afishyke/DACS/delay_justification/eda_outputs/plots/metric_derivative_energy_by_class.png

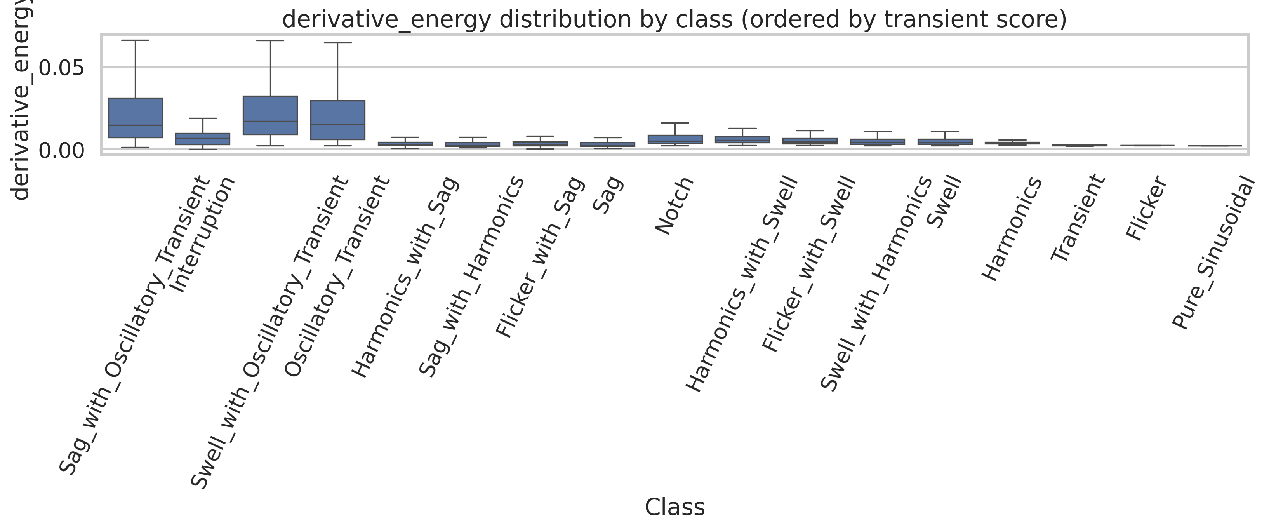
delay_justification/eda_outputs/plots/metric_derivative_energy_by_class.png
