afishyke/DACS/delay_justification/eda_outputs/plots/metric_high_freq_energy_ratio_by_class.png

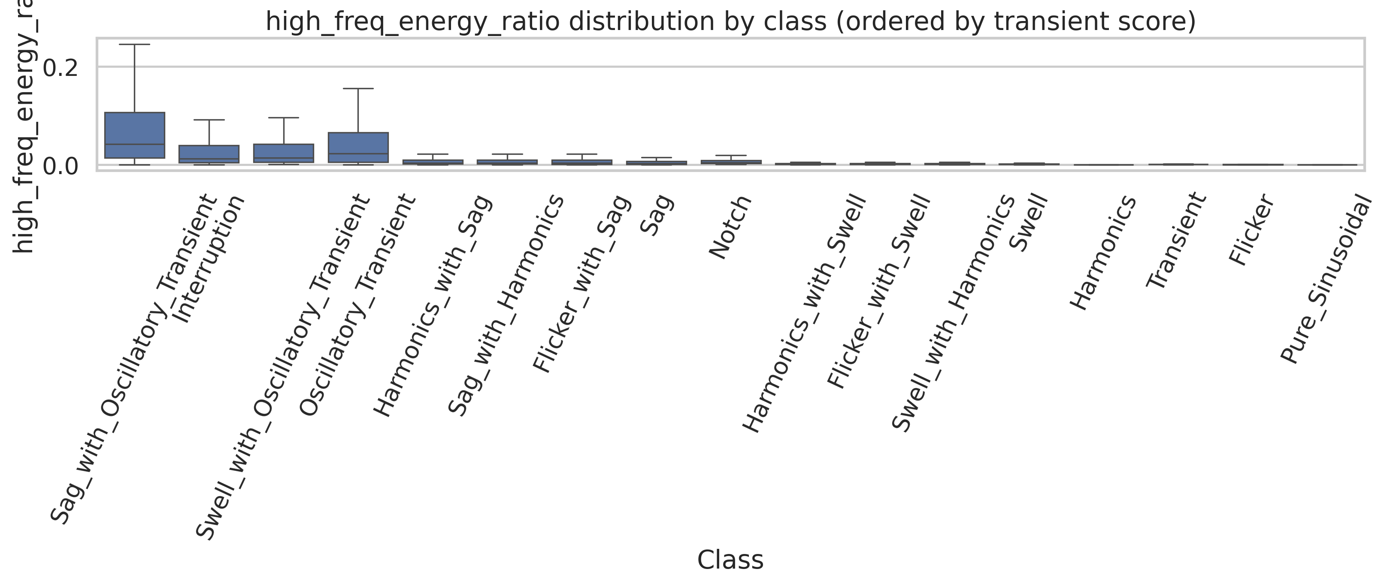
delay_justification/eda_outputs/plots/metric_high_freq_energy_ratio_by_class.png
