afishyke/DACS/delay_justification/eda_outputs/plots/metric_local_peak_change_by_class.png

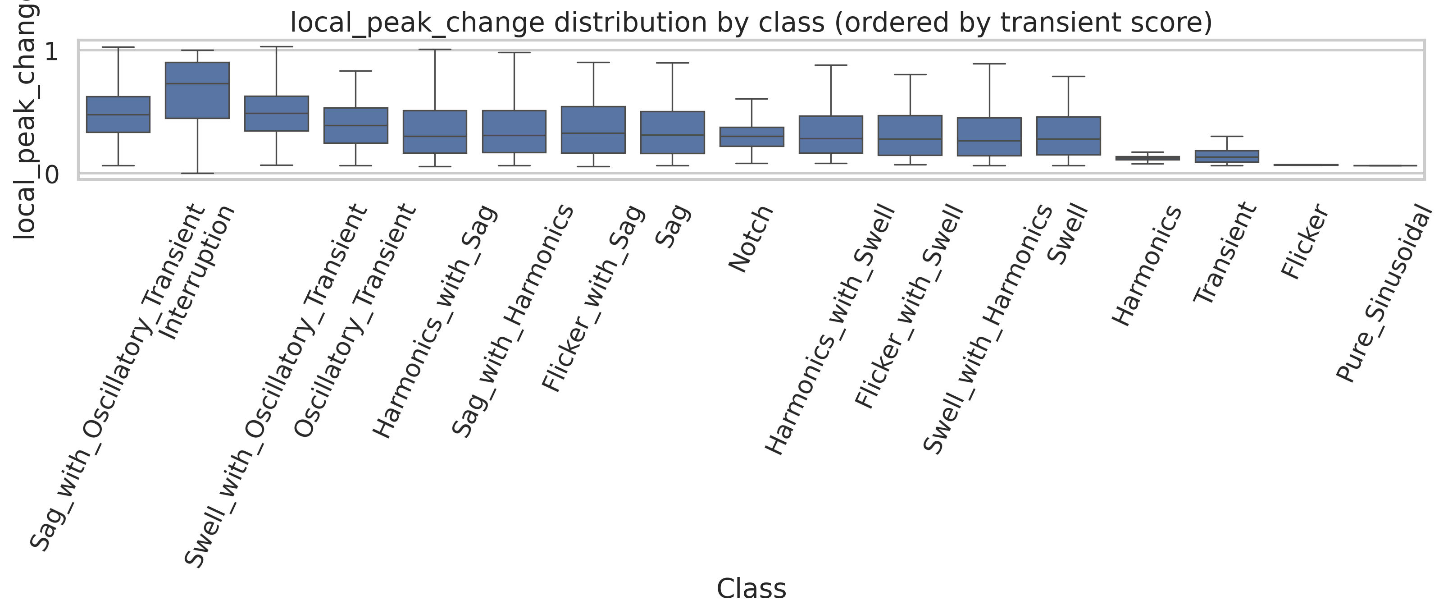
delay_justification/eda_outputs/plots/metric_local_peak_change_by_class.png
