afishyke/DACS/delay_justification/eda_outputs/plots/metric_transient_energy_proxy_by_class.png

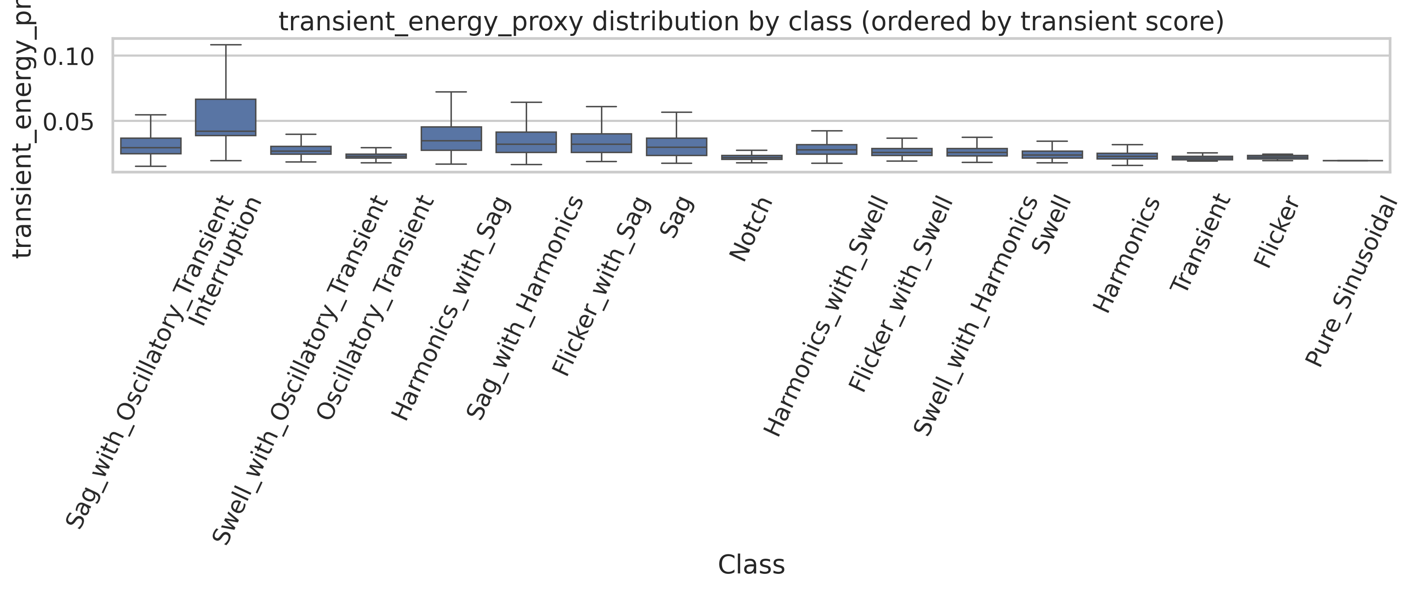
delay_justification/eda_outputs/plots/metric_transient_energy_proxy_by_class.png
