afishyke/DACS/delay_justification/eda_outputs/plots/overlay_harmonics_flicker_related_classes.png

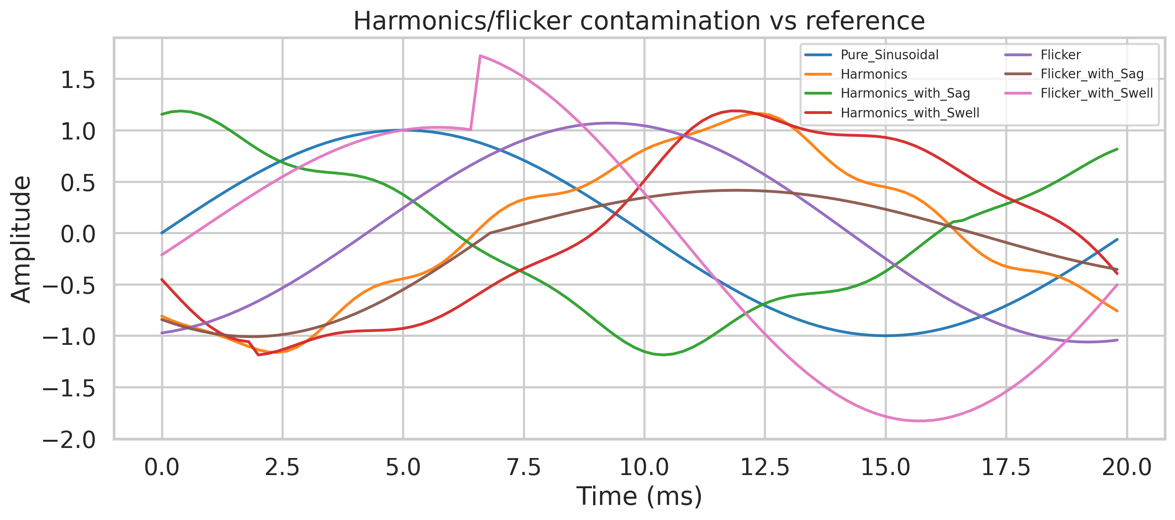
delay_justification/eda_outputs/plots/overlay_harmonics_flicker_related_classes.png
