afishyke/DACS/delay_justification/eda_outputs/plots/overlay_sag_swell_related_classes.png

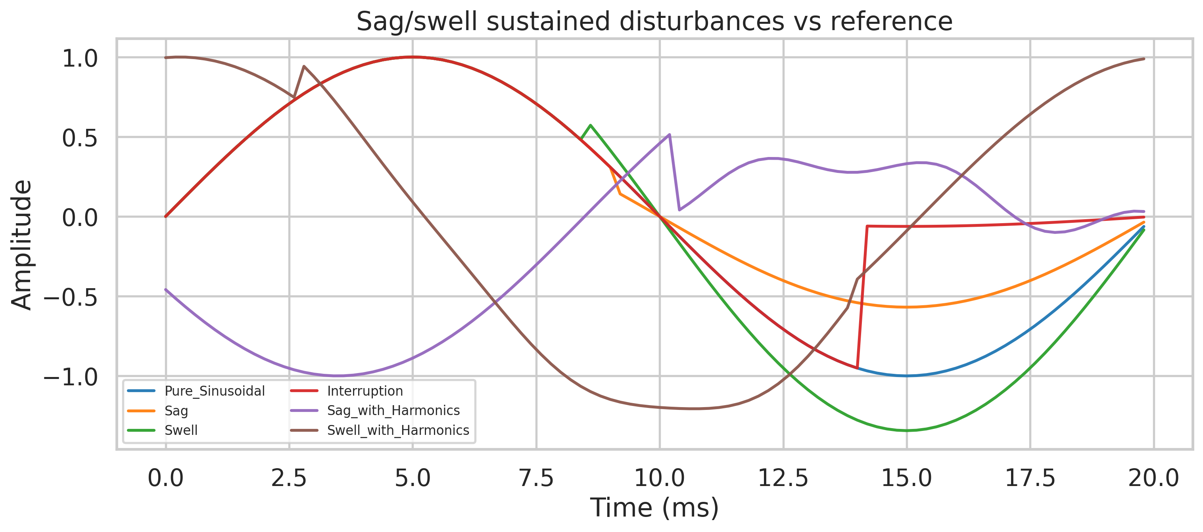
delay_justification/eda_outputs/plots/overlay_sag_swell_related_classes.png
