afishyke/DACS/delay_justification/eda_outputs/plots/per_class_3_representatives/Harmonics_with_Sag_three_representatives.png

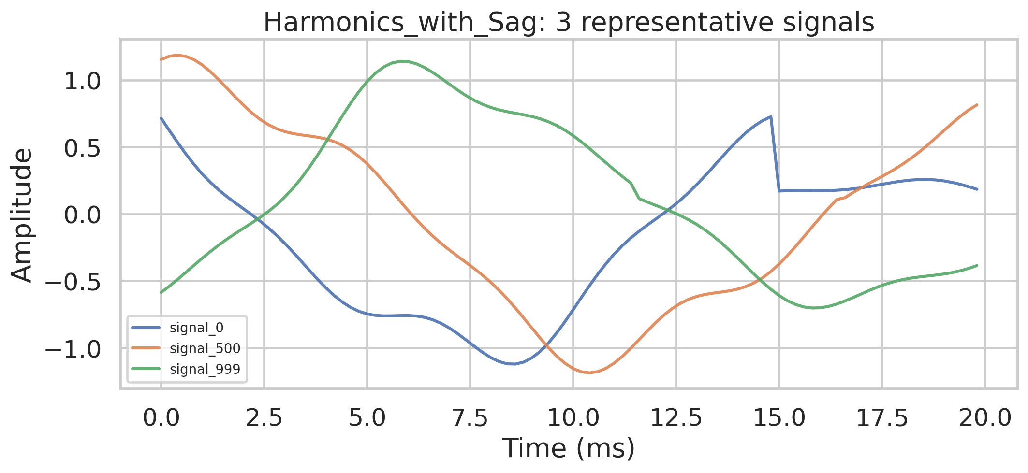
delay_justification/eda_outputs/plots/per_class_3_representatives/Harmonics_with_Sag_three_representatives.png
