afishyke/DACS/delay_justification/eda_outputs/plots/per_class_3_representatives/Sag_with_Oscillatory_Transient_three_representatives.png

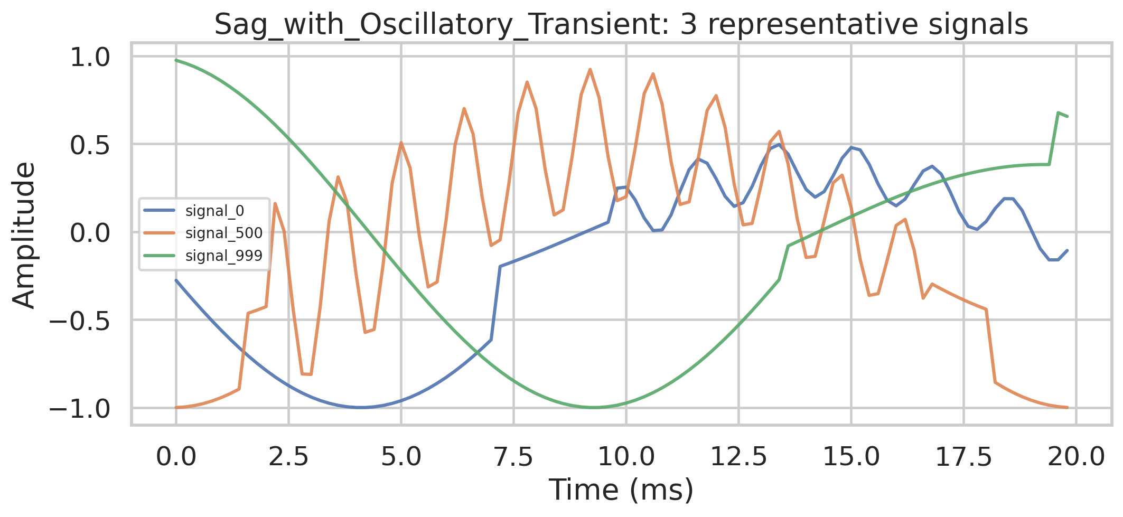
delay_justification/eda_outputs/plots/per_class_3_representatives/Sag_with_Oscillatory_Transient_three_representatives.png
