afishyke/DACS/hardware/breadboard/WhatsApp Image 2026-04-08 at 23.20.41.jpeg

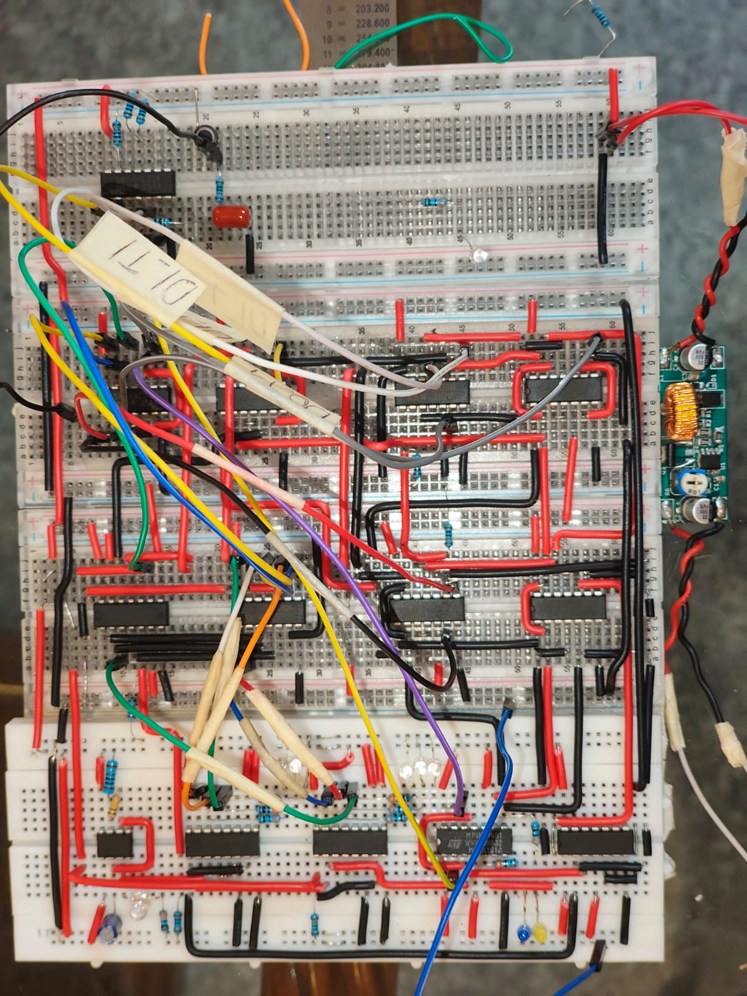
hardware/breadboard/WhatsApp Image 2026-04-08 at 23.20.41.jpeg
