afishyke/DACS/grid_ok_generation/comparator_grid_ok.asc

B1: bv; V = 80*time*sin(2*pi*50*time)
C1: cap; 1000µF
C2: cap; 0.33µF
D1: diode; 1N4148
D2: diode; 1N4148
D3: diode; 1N4148
D4: diode; 1N4148
R1: res; 82K
R2: res; 10K
R3: res; 8.2K
R4: res; 4.7K
R5: res; 9.1K
R6: res; 3.3K
R7: res; 10K
U1: LM393; LM2903B
U2: LM393; LM2903B
V2: voltage; 5V
Named nets: 0
.tran 0.3
